jahneff/CS461/Writeups/Individual Assignments/Tech Review Rough Draft/Brandon/ellibran_tech_review_rough_draft.tex

\documentclass[IEEEtran,letterpaper,10pt,titlepage,fleqn,draftclsnofoot,onecolumn]{article}
%notitlepage vs titlepage
%fleqn left align

%\usepackage{nopageno} %no page numbers
\usepackage{indentfirst}
\usepackage{alltt}                                           
\usepackage{float}
\usepackage{color}
\usepackage{url}

\usepackage{graphicx}                                        
\usepackage{amssymb}                                         
\usepackage{amsmath}                                         
\usepackage{amsthm}                                          

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

\geometry{textheight=9.5in, textwidth=7in} 

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

\def\name{Brandon Ellis}
\def\class{CS 461}
\def\assignment{Technology Review}

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

\section{Soil Moisture}
\subsection{Overview}

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

\subsection{Criteria}

The only core piece of criteria is the collection of soil moisture data. Further aspects of this device that will be considered is the working temperature, power use, and cost. 

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

\vspace{1mm}

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

\vspace{1mm}

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

\subsubsection{SparkFun Soil Moisture Sensor[3]}
\textit{5V Power | Consumption Not Given | \$5.95}

\vspace{1mm}

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

\subsection{Discussion}

Unfortunately, the best choices for this sensor do not list their operational ranges and accuracies. Under the core assumption that all do in fact measure soil moisture in a quantitative method, we are left with the power use, cost, and connectivity to define which fills the task best. The Phantom YoYo does have the lowest cost, but the temperature range could be a problem during very cold winters. It also has the lowest power consumption out of all of these candidates. The Icstation has the largest cost and the largest noted power consumption. For this, the only decernable benefit that we would get is the ability to place the probe a distance from the device, as it comes with a connecting cable. The final choice is the SparkFun Soil Moisture Sensor. While this device does have assumed Arduino connectivity, it lists no other information about the sensor. Further the brand that it is associated with, and subsequent board that is in a kit with it, is not recommended by our client.

\clearpage

\subsection{Conclusion}

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

\section{Air Temperature \& Humidity}
\subsection{Overview}

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

\subsection{Criteria}

The required functionality that this this device needs to have is simply the ability to record the air temperature and humidity. Beyond that the only other pieces that come into play are its power consumption, the cost of the component, and any additional features it may bring. There is however a stronger weight on the topic of power consumption.

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

\vspace{1mm}

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

\vspace{1mm}

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

\clearpage

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

\vspace{1mm}

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

\subsection{Discussion}

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

\subsection{Conclusion}

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

\section{Microcontroller}
\subsection{Overview}

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

\subsection{Criteria}

The most important aspect of this board is its power consumption. This board will be powered by a solar panel with a backup battery, as such the microcontroller cannot be a goliath. Other criteria that will have weight on this choice is the operating voltage, any wireless connectivity the board may have, and the method of powering.

\clearpage

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

\vspace{1mm}

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

\vspace{1mm}

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

\vspace{1mm}

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

\subsection{Discussion}

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

\subsection{Conclusion}

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

\clearpage

\section{References}
[1] https://www.amazon.com/Phantom-YoYo-compatible-Sensitivity-Moisture/dp/B00AFCNR3U

\vspace{1mm}

[2]https://www.amazon.com/Icstation-Soil-Moisture-Sensor-Module/dp/B074XFNK7H/

\vspace{1mm}

[3]https://www.sparkfun.com/products/13322

\vspace{1mm}

[4]https://www.sparkfun.com/products/13676

\vspace{1mm}

[5]https://cdn.sparkfun.com/assets/learn\_tutorials/4/1/9/BST-BME280\_DS001-10.pdf

\vspace{1mm}

[6]https://www.sparkfun.com/products/14348

\vspace{1mm}

[7]https://cdn.sparkfun.com/assets/learn\_tutorials/1/4/3/CCS811\_Datasheet-DS000459.pdf

\vspace{1mm}

[8]https://www.sparkfun.com/products/13674

\vspace{1mm}

[9]https://cdn.sparkfun.com/datasheets/Sensors/Weather/Si7021.pdf

\vspace{1mm}

[10]https://cdn.sparkfun.com/datasheets/Sensors/Pressure/MPL3115A2.pdf

\vspace{1mm}

[11]https://www.sparkfun.com/products/13321

\vspace{1mm}

[12]https://store.arduino.cc/usa/arduino-mkr1000

\vspace{1mm}

[13]https://store.arduino.cc/usa/arduino-nano

\vspace{1mm}

[14]http://www.atmel.com/images/Atmel-8271-8-bit-AVR-Microcontroller-ATmega48A-48PA-88A-88PA-168A-168PA-328-328P\_datasheet\_Complete.pdf

\vspace{1mm}

[15]https://store.arduino.cc/usa/arduino-yun-mini

\end{document}
