jahneff/CS461/Writeups/Group Assignments/Progress Reports/Winter Term/Final Report/Progress_Report_Winter_Final.pdf

# Green Smart Gardening Systems

# Winter Midterm Progress Report

## Brandon Ellis | Jiayu Han | Jack Neff

# Progress Report

## - Purpose of this Document ● Audience

Brandon Ellis | ● My Work
| ● Recap
| ● Week 7 – 10
| ● Demo
| ● Future Work

# Recap

## - Winter Break ● Week 1 – 6

# Week 7

### TA Meeting

- N/A

### Client Meeting

- Recap
- Break Report
- Schedule

### Work Addressed

- BME280 Testing

# Week 8

### TA Meeting

- First Meeting

### Client Meeting

- BME280 Pictures
- SD Card Reader

### Work Addressed

- BME280 Testing

# Week 9

### TA Meeting

- Schedule

### Client Meeting

- Valid Wiring
- SPI vs I2C
- Design Doc
- Intel Logo

### Work Addressed

- BME280 Pictures
- Schedule
- SD Card Research

# Week 10

### TA Meeting

- Database Connection

### Client Meeting

- Update on BME280
- Database Connection

### Work Addressed

- BME280 Solution

# Demo [Wiring]

# Demo [Data Flow]

# What’s Next?

### Work to Do

- Sensor
- Board Logic
- Testing

Jack Neff | ● | Purpose: Describe and demonstrate
| | current functionality of project.

## - Audience: Instructors Kirsten Winters

| | and D. Kevin McGrath, Intel clients Po-
| | Cheng Chen, Satoshi Suzuki, and
| | Eduardo Alban

Jack Neff | ● My Work
| ● Recap
| ● Week 7 – 10
| ● Demo
| ● Future Work

# My Work

## - Front end user interface

## - Back end HTTP server

## - Back end data storage

Recap | ● Week 1 – 6
- VM

## - LAMP

## - Database connections

## - Dummy data

# Week 7

### Action Items

- Research and experiment with FusionCharts

### Work Addressed

- Set up vineyard visit
- Connected VM to local machine through Filezilla
- Switched from d3.js to FusionCharts

# Week 8

### Work Addressed

- Created preliminary charts
- Visited vineyard

### Action Items

- Begin design of homepage
- General smart gardening system research
- Contact Picovale

# Week 9

### Work Addressed

- Researched automated gardening systems

### Action Items

- Continue designing homepage
- Contact Picovale
- Connect Arduino to campus networks

# Week 10

### Work Addressed

- Contacted Picovale
- Tweaked homepage layout
- Updated sensor array design

### Action Items

- Continue to design homepage
- Connect Arduino to Campus networks
- Meet with group to create user study

# Demo [Dummy Data + Database + Web site]

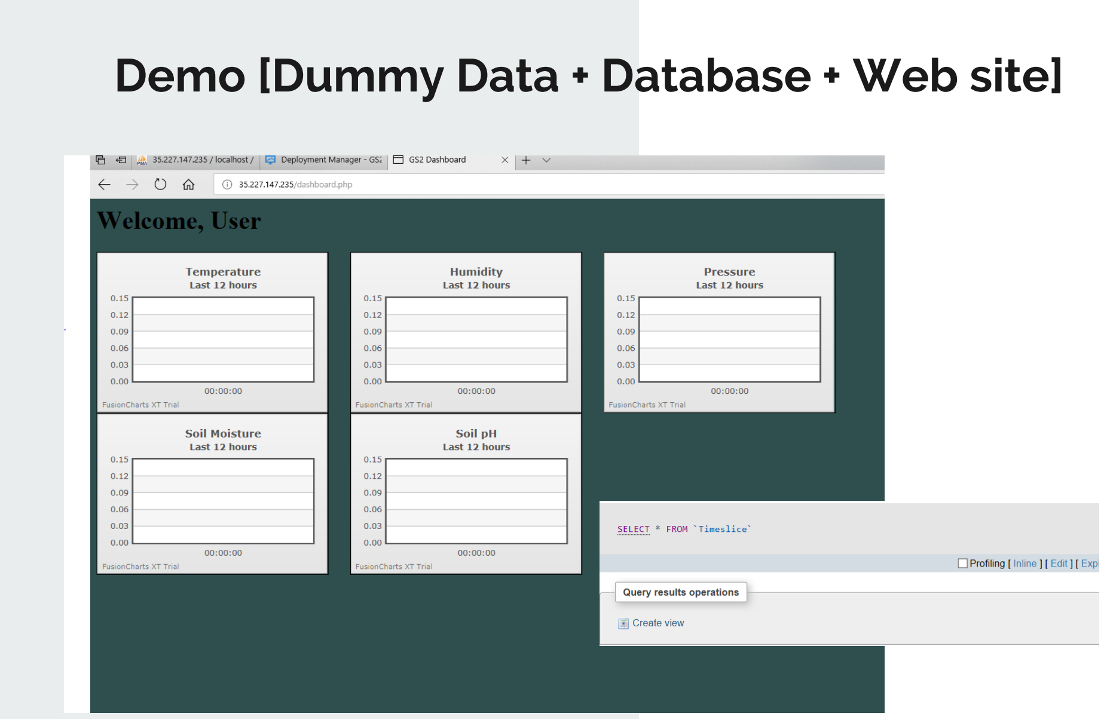
[picture p17: page 20]

# Demo [Dummy Data + Database + Web site]]

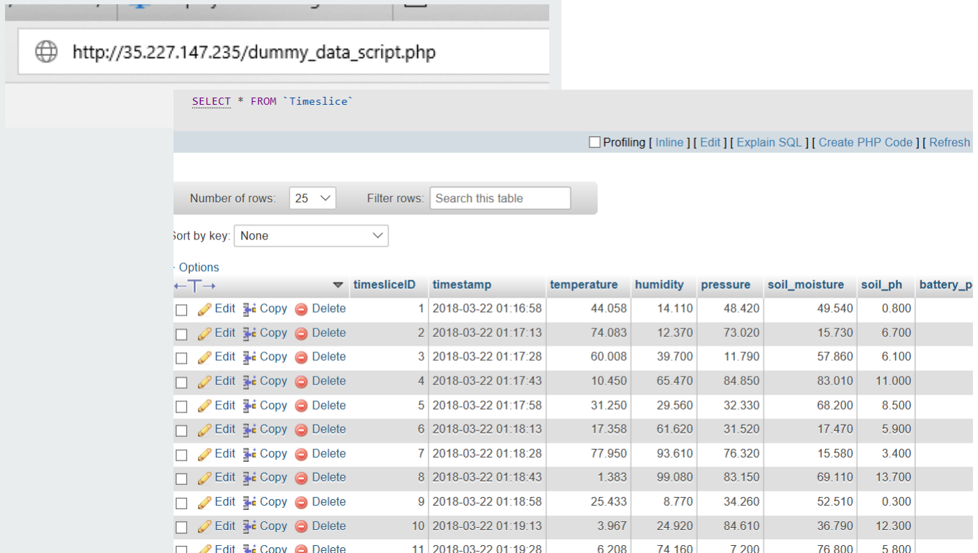
[picture p18: figure]

# Demo [Dummy Data + Database + Web site]]

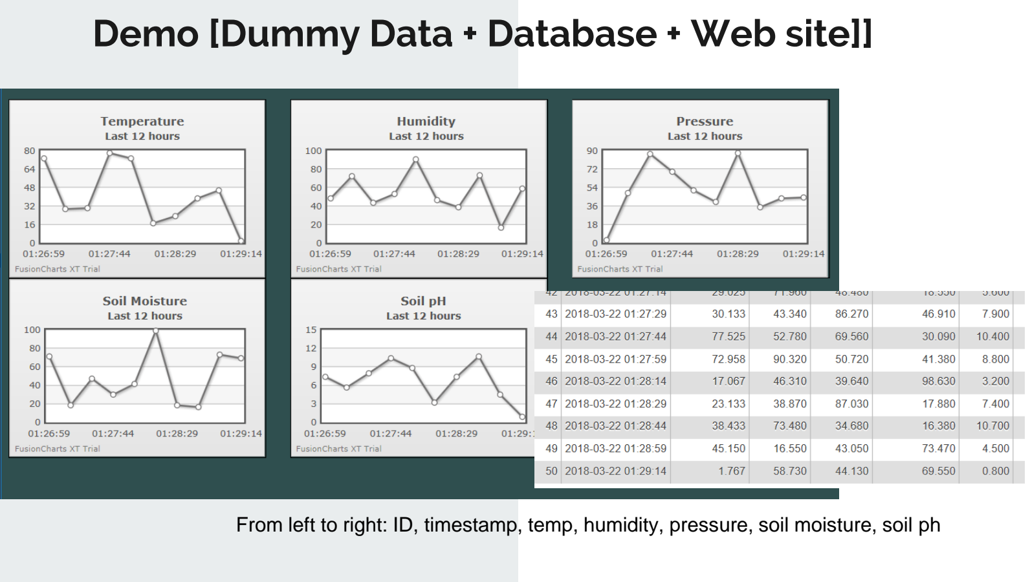
[picture p19: page 22]

### From left to right: ID, timestamp, temp, humidity, pressure, soil moisture, soil ph

# What’s Next?

### Work to Do

- User studies
- Web site
- Graphs
- Other functionality/research

Jiayu Han | ● My Work
| ● Recap
| ● Week 7 – 10
| ● Demo
| ● Future Work

My Work | ● Wi-Fi
| ● Power ● Packaging(3D Model/Print)

Recap | ● Week 1 – 6

# Week 7

### TA Meeting

- Alpha Version(pushed)

### Client Meeting

- Packaging Rough Draft
- Updated Shopping List

### Work Addressed

- Soil sensor Location on Packaging
- Solar Panel Voltage(6v to 5v)

# Week 8

### TA Meeting

- Alpha Version(pushed)
- 3D HUBS

### Client Meeting

- Vineyard visit

### Work Addressed

- Soil Sensor Location Change

# Week 9

### TA Meeting

- Alpha Version(pushed)

### Client Meeting

- 3D Print(Intel/OSU/3D Hubs)
- BME Sensor Location Test

### Work Addressed

- Packaging
- Test Power System

# Week 10

### TA Meeting

- Alpha Version showed

### Client Meeting

- Packaging
- Updates
- Alpha Version

### Work Addressed

- Packaging
- Battery Percentage Display
- Sensors

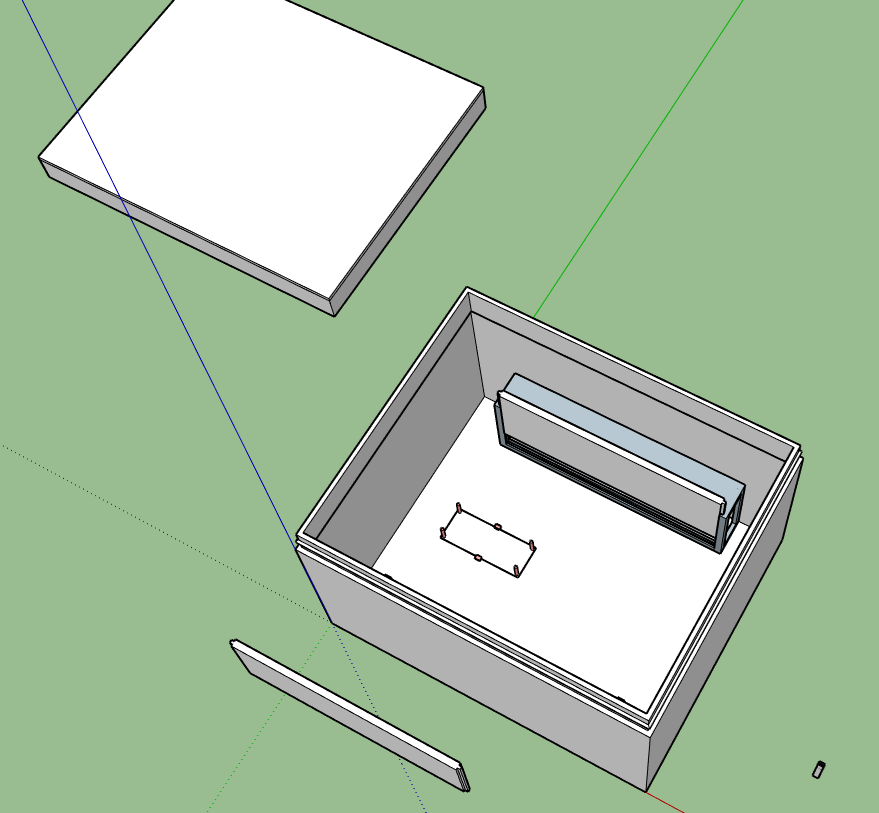
[picture p20: figure]

# Demo [3D Model]

# What’s Next?

### Work to Do

- 3D Model(Polishing/Print)
- Battery Percentage
- Testing
