jahneff/CS461/Writeups/Group Assignments/Design Document/ezo_hookup.png

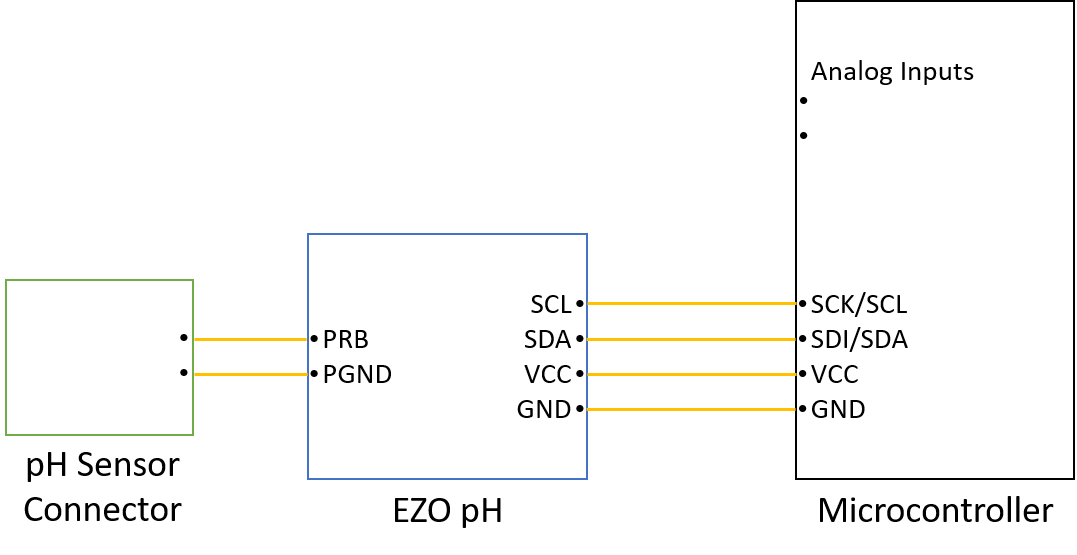
Writeups/Group Assignments/Design Document/ezo_hookup.png
