jahneff/CS461/MicroController/GSGS_Core/secrets.h

#define SECRET_SSID ""
#define SECRET_PASS ""

/* ##############
 * ssid List:
 *  "The Promised Lan"
 *    Brandon Home
 *    Pass Required
 *  "Visitor"
 *    Kelly Open
 *    No Pass
 * ############## */
